krzys9876/ZX_Spectrum_diy/Kicad5/zx2_backplane/zx2_backplane_B.pdf

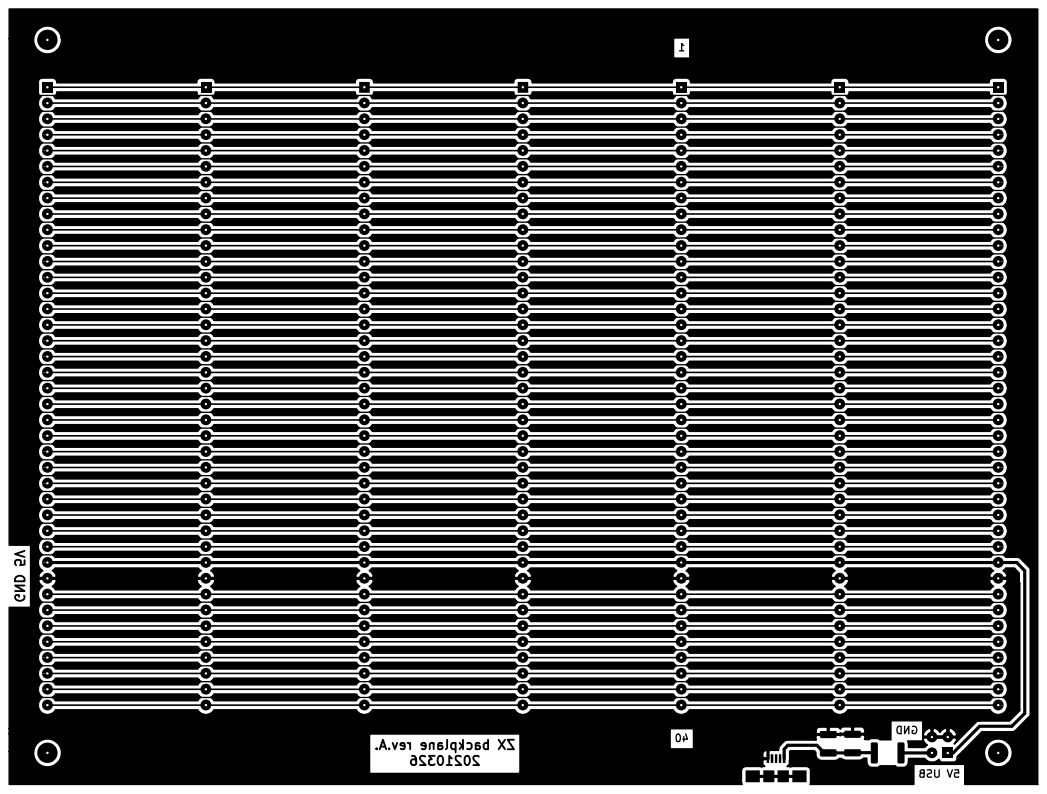
[picture p13: page 1]
