krzys9876/ZX_Spectrum_diy/Kicad5/zx2_clock/zx2_clock_B_err.pdf

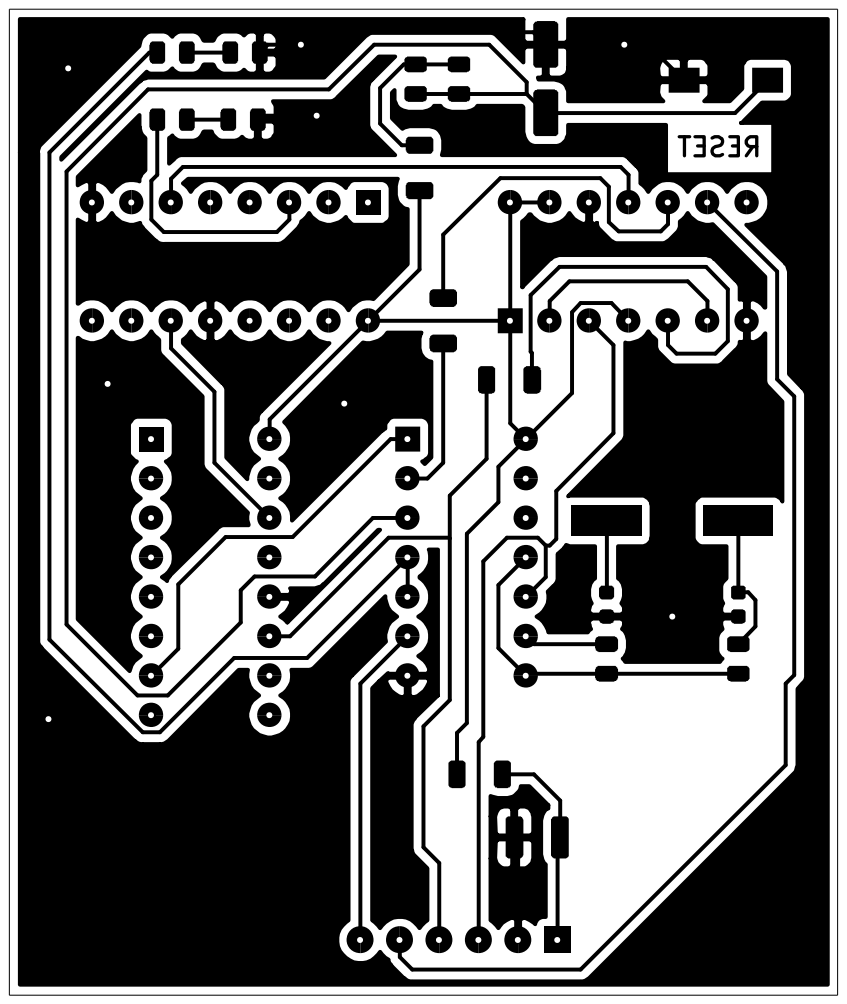
[picture p14: page 1]
