krzys9876/ZX_Spectrum_diy/Kicad5/zx2_clock/zx2_clock_col_err.pdf

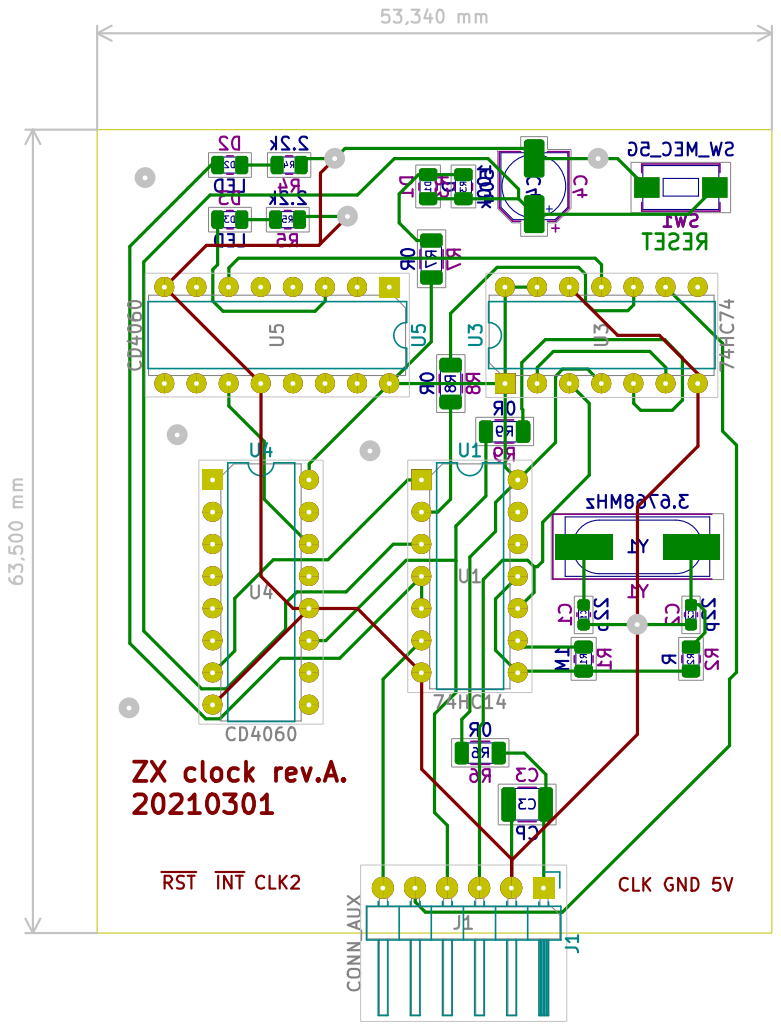
[picture p15: page 1]
