krzys9876/ZX_Spectrum_diy/Kicad5/zx2_clock/zx2_clock_F_err.pdf

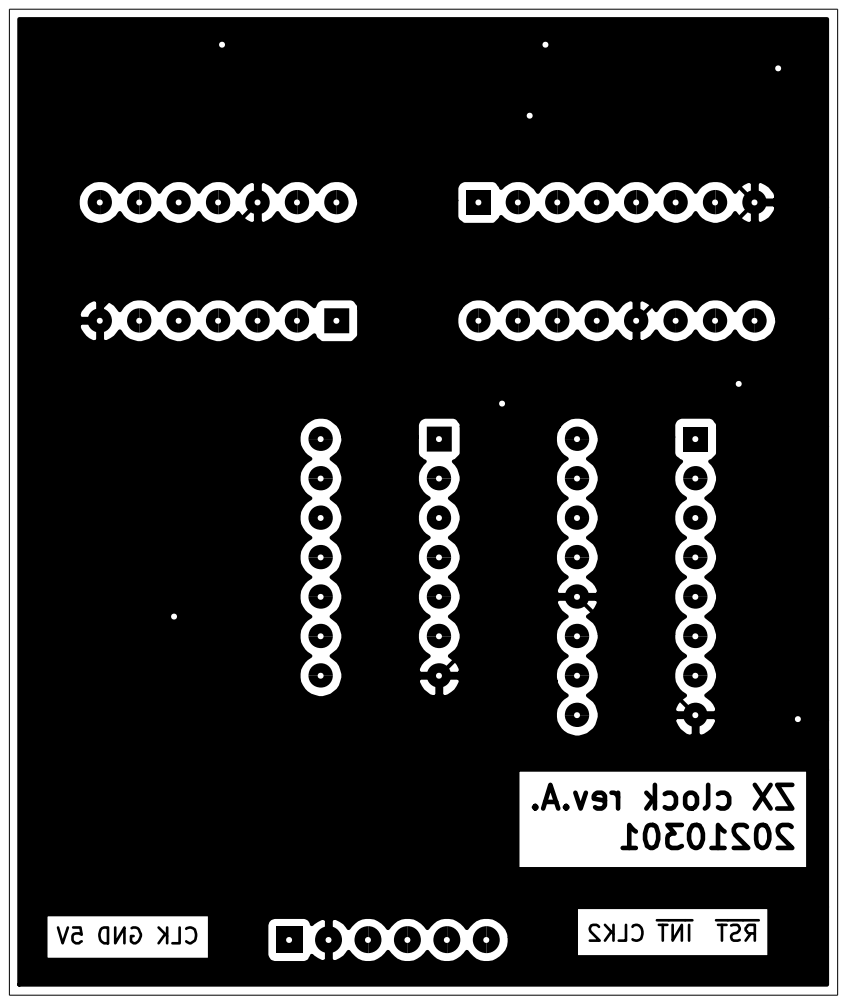
[picture p16: page 1]
