krzys9876/ZX_Spectrum_diy/Kicad5/zx2_cpu/zx2_cpu_B.pdf

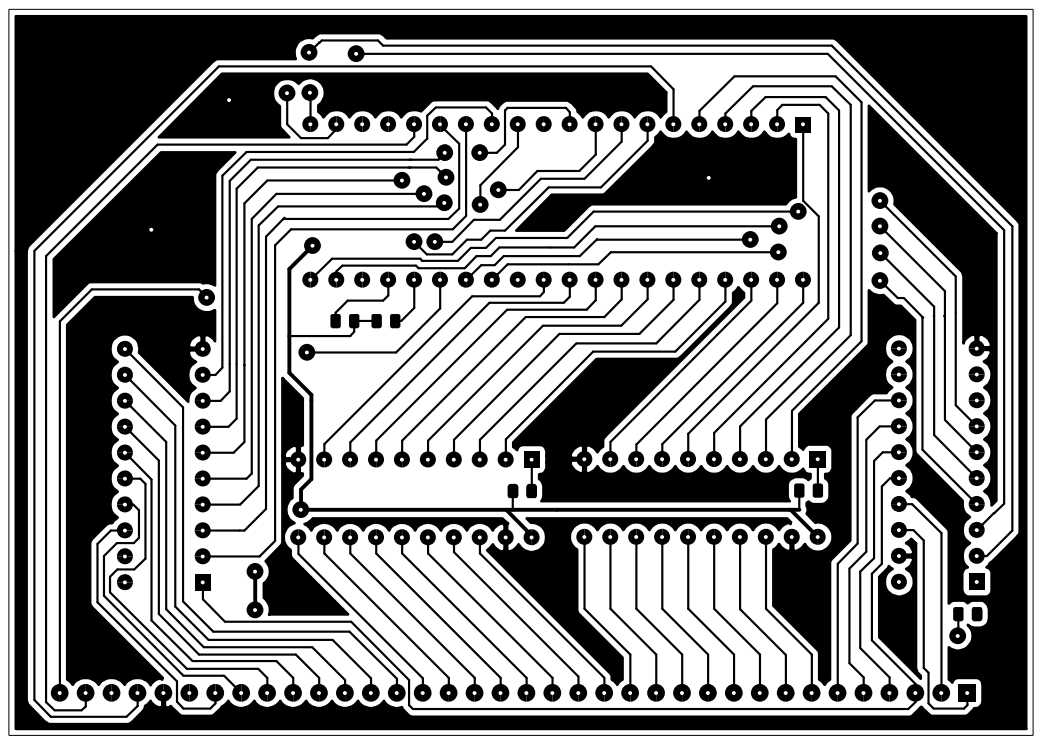
[picture p17: page 1]
