krzys9876/ZX_Spectrum_diy/Kicad5/zx2_cpu/zx2_cpu_col.pdf

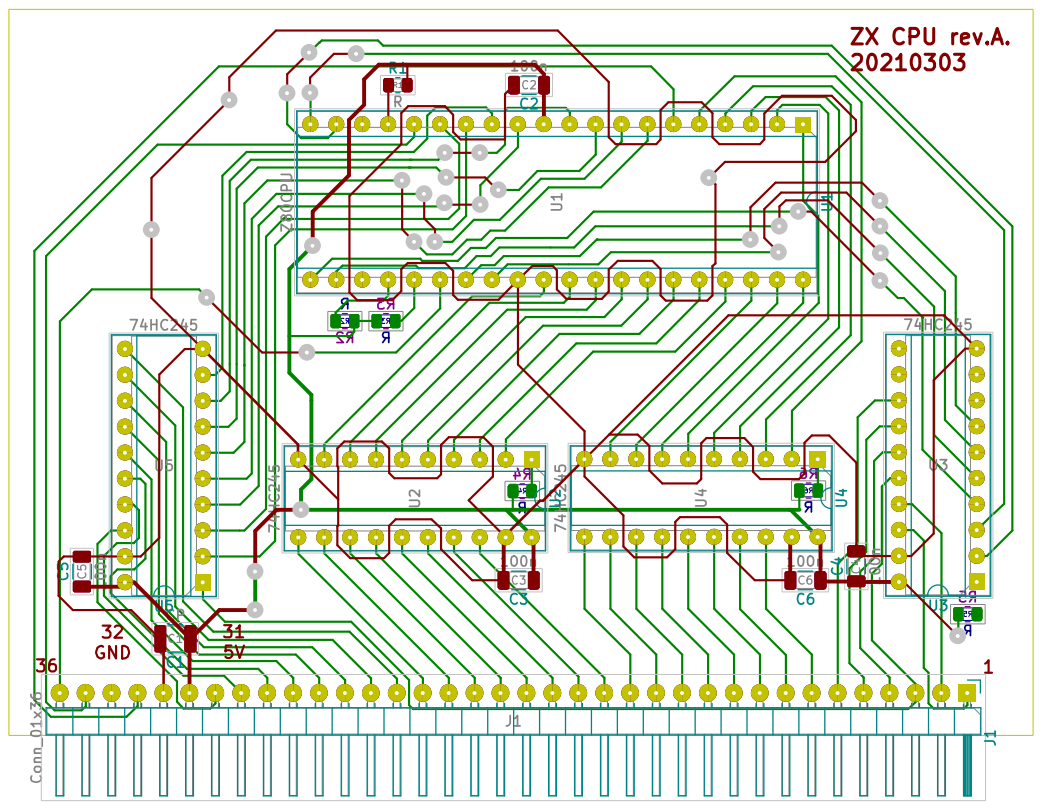
[picture p18: page 1]
