krzys9876/ZX_Spectrum_diy/Kicad5/zx2_cpu/zx2_cpu_F.pdf

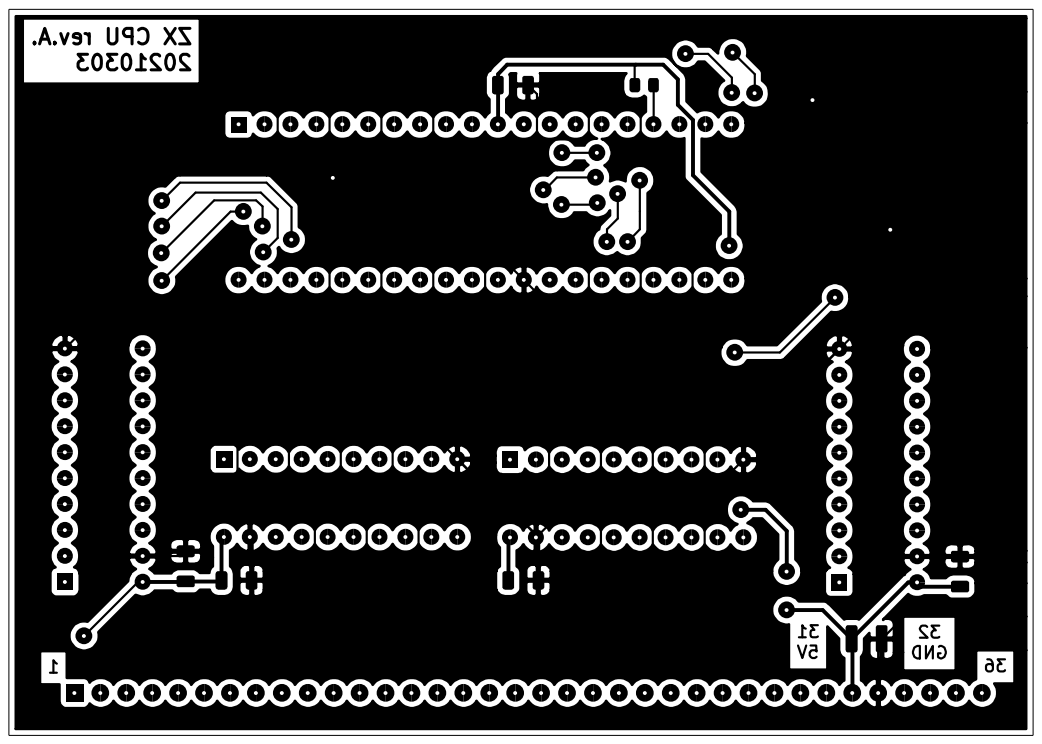
[picture p19: page 1]
