krzys9876/ZX_Spectrum_diy/Kicad5/zx2_fpga_int/zx2_fpga_int_B.pdf

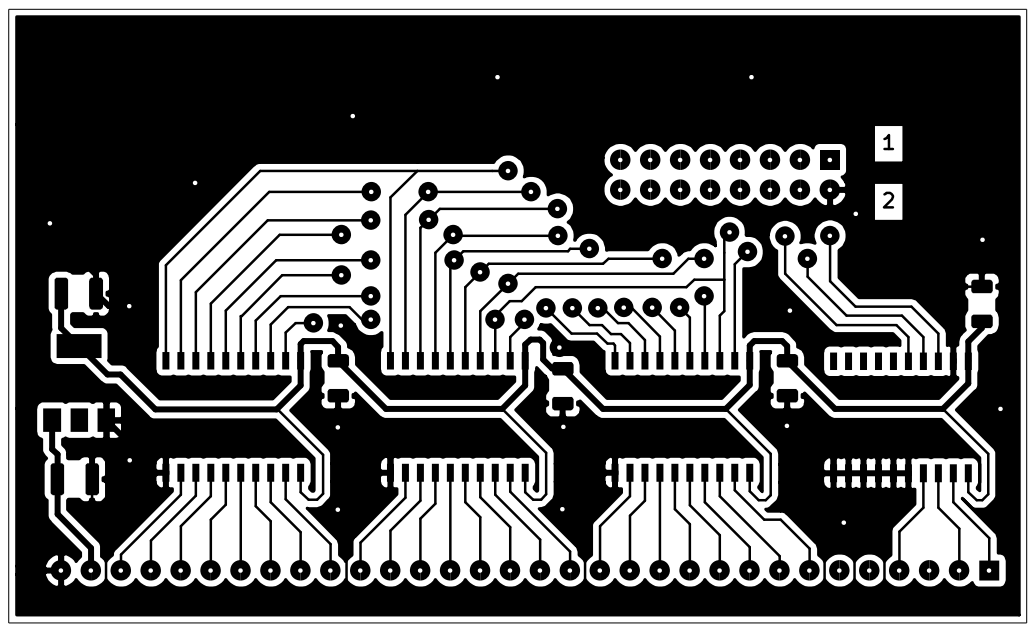
[picture p20: page 1]
