krzys9876/ZX_Spectrum_diy/Kicad5/zx2_fpga_int/zx2_fpga_int_col.pdf

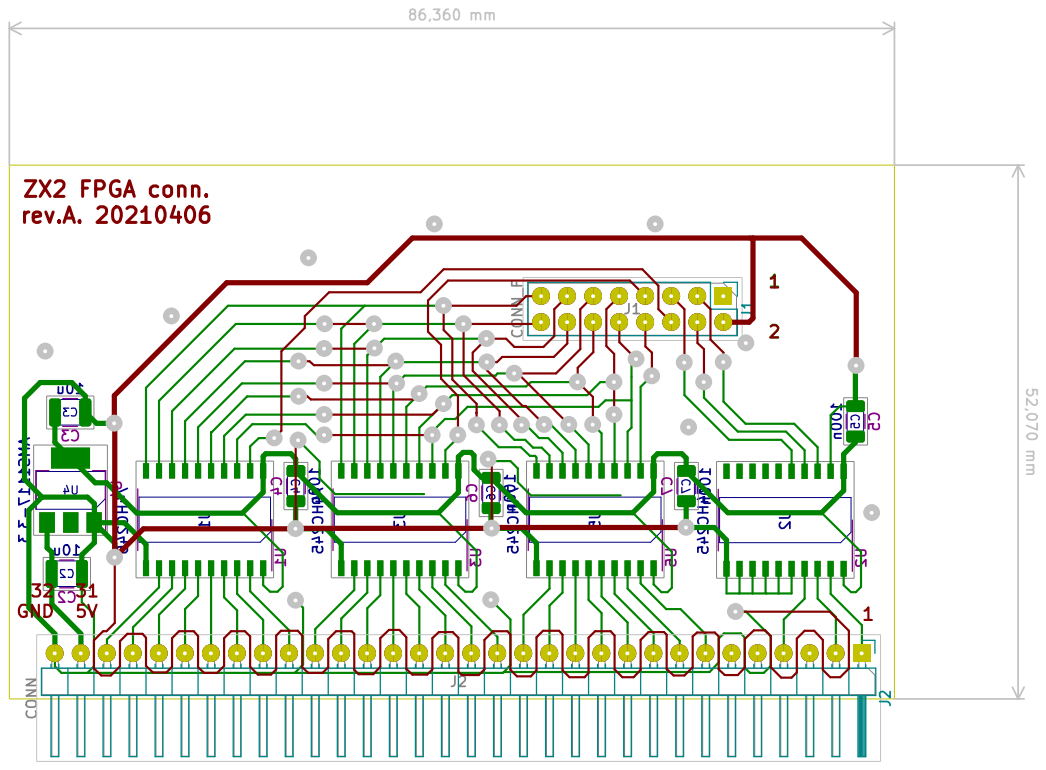
[picture p21: page 1]
