krzys9876/ZX_Spectrum_diy/Kicad5/zx2_fpga_int/zx2_fpga_int_F.pdf

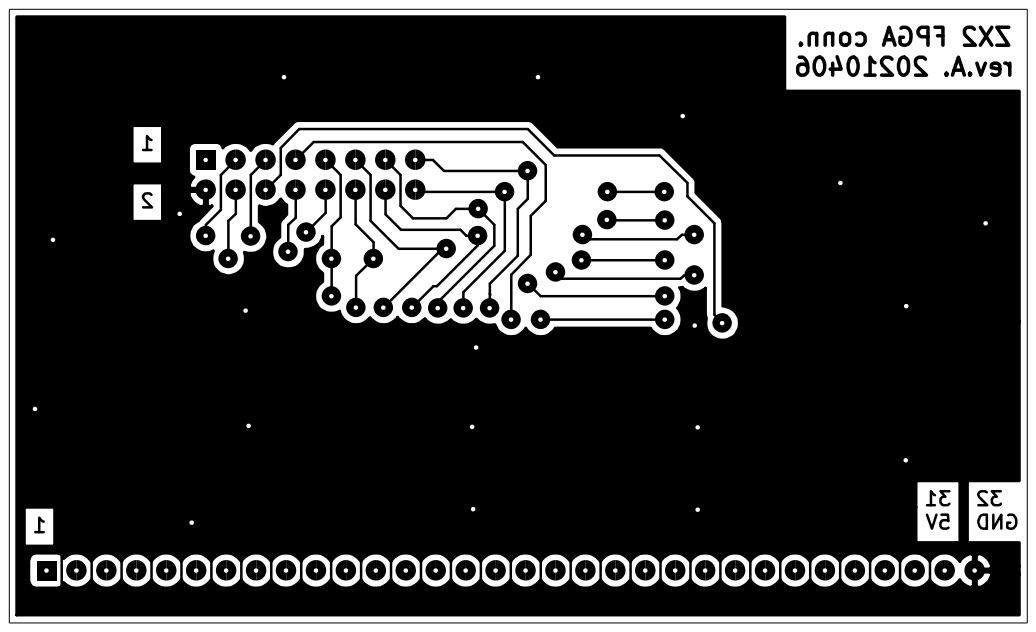
[picture p22: page 1]
