krzys9876/ZX_Spectrum_diy/Kicad5/zx2_keyb_conn/zx2_keyb_conn_B_revB.pdf

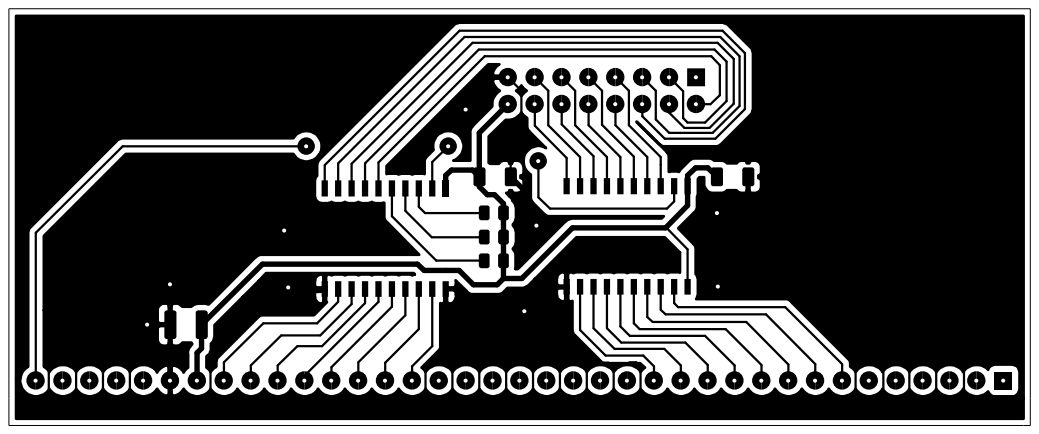
[picture p25: page 1]
