krzys9876/ZX_Spectrum_diy/Kicad5/zx2_keyb_conn/zx2_keyb_conn_col.pdf

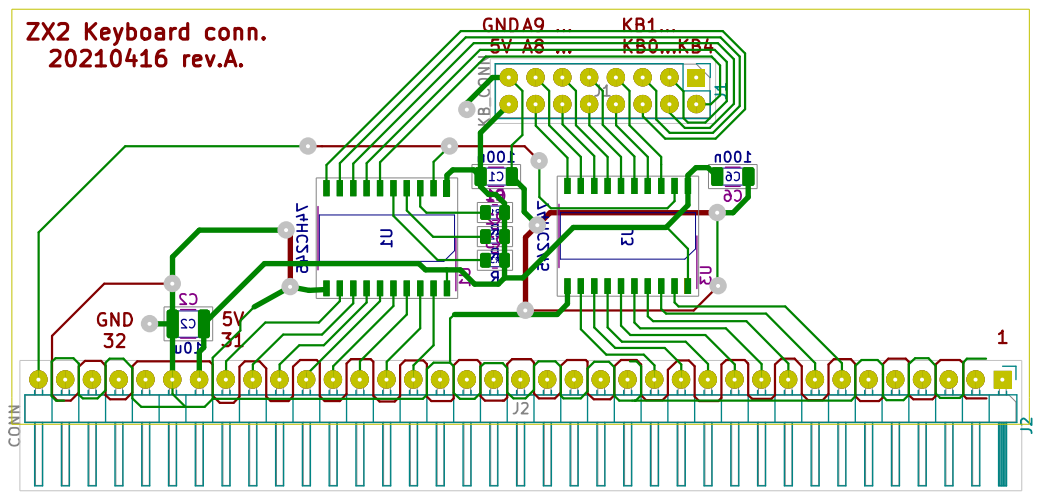
[picture p26: page 1]
