krzys9876/ZX_Spectrum_diy/Kicad5/zx2_keyb_conn/zx2_keyb_conn_col_revB.pdf

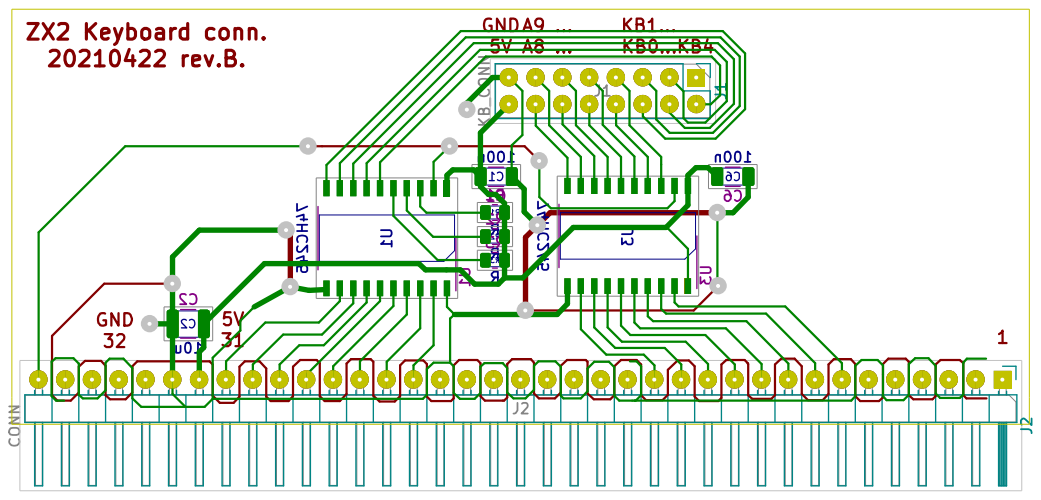
[picture p27: page 1]
