krzys9876/ZX_Spectrum_diy/Kicad5/zx2_keyb_conn/zx2_keyb_conn_F.pdf

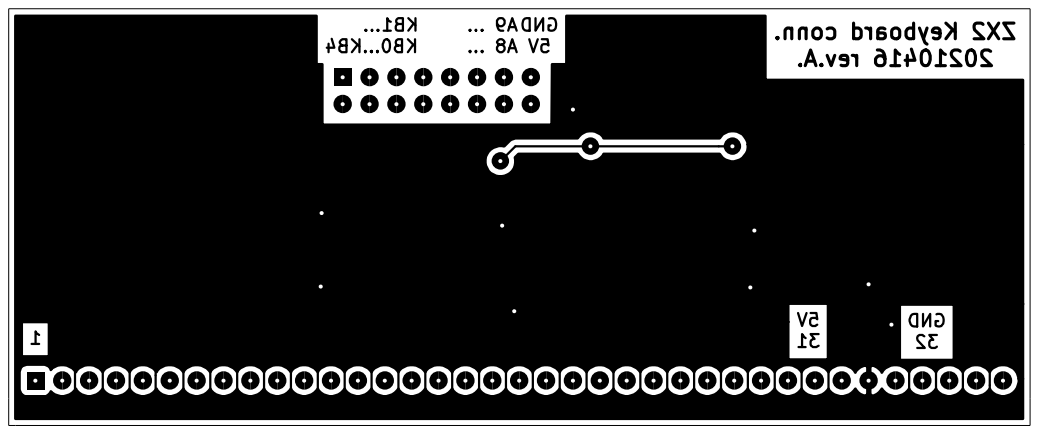
[picture p28: page 1]
