krzys9876/ZX_Spectrum_diy/Kicad5/zx2_keyb_idc/zx2_keyb_idc_F.pdf

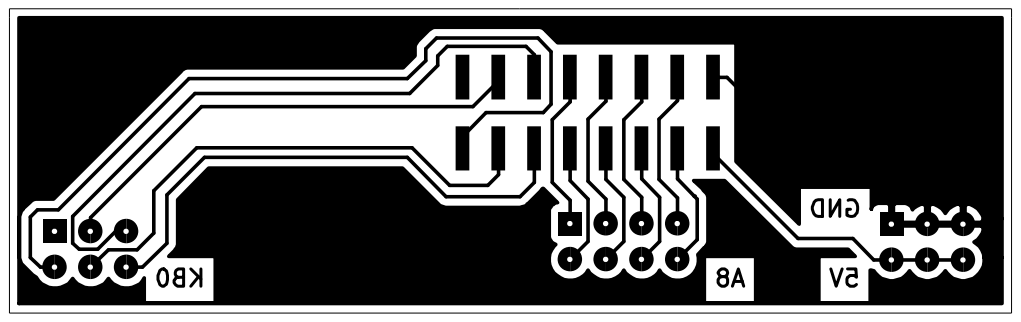
[picture p30: page 1]
