krzys9876/ZX_Spectrum_diy/Kicad5/zx2_mem/zx2_mem_B.pdf

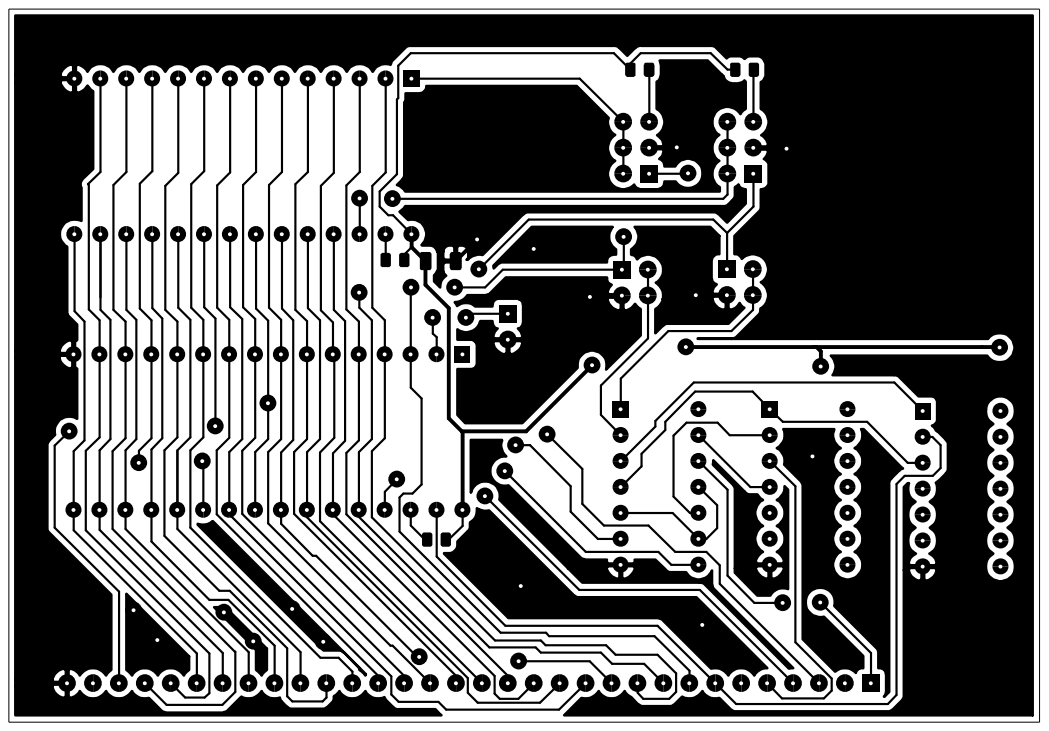
[picture p31: page 1]
