krzys9876/ZX_Spectrum_diy/Kicad5/zx2_mem/zx2_mem_B_rB.pdf

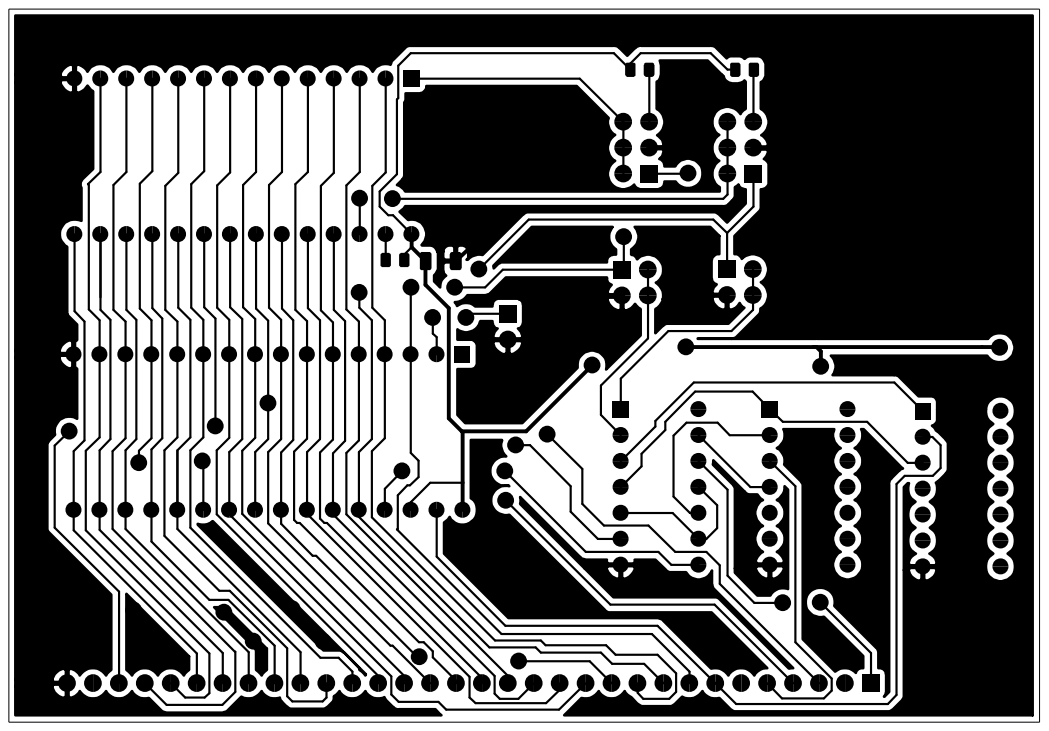
[picture p32: page 1]
