krzys9876/ZX_Spectrum_diy/Kicad5/zx2_mem/zx2_mem_col.pdf

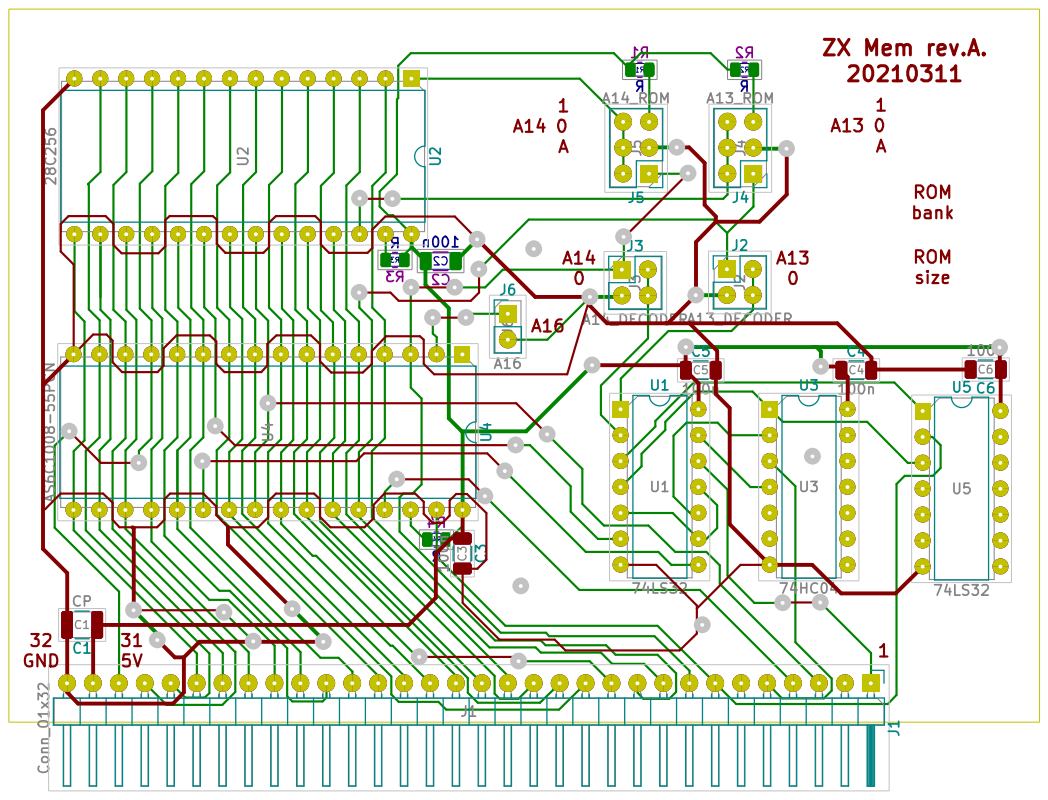
[picture p33: page 1]
