krzys9876/ZX_Spectrum_diy/Kicad5/zx2_mem/zx2_mem_col_rB.pdf

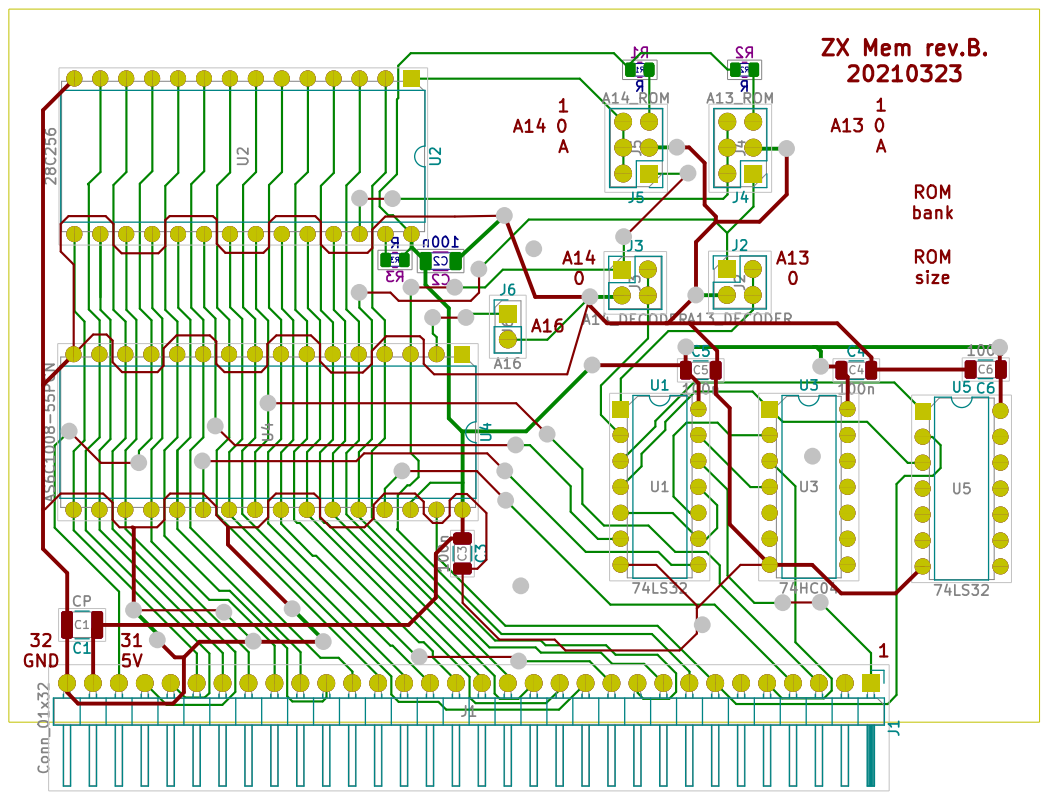
[picture p34: page 1]
