krzys9876/ZX_Spectrum_diy/Kicad5/zx2_mem/zx2_mem_F.pdf

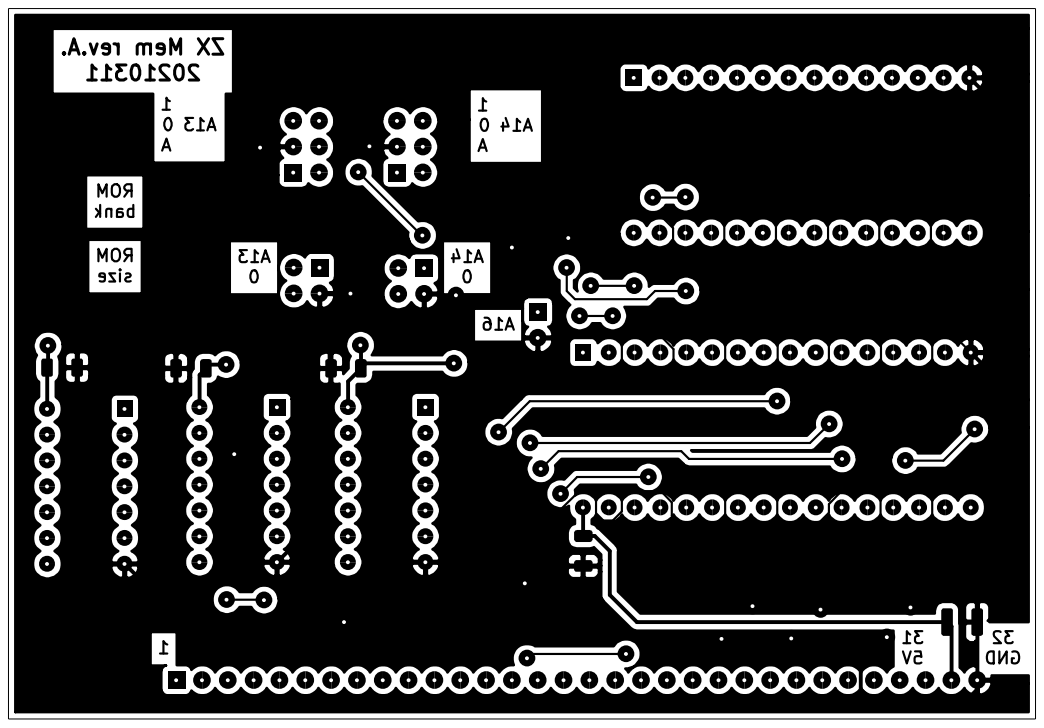
[picture p35: page 1]
