krzys9876/ZX_Spectrum_diy/Kicad5/zx2_mem/zx2_mem_F_rB.pdf

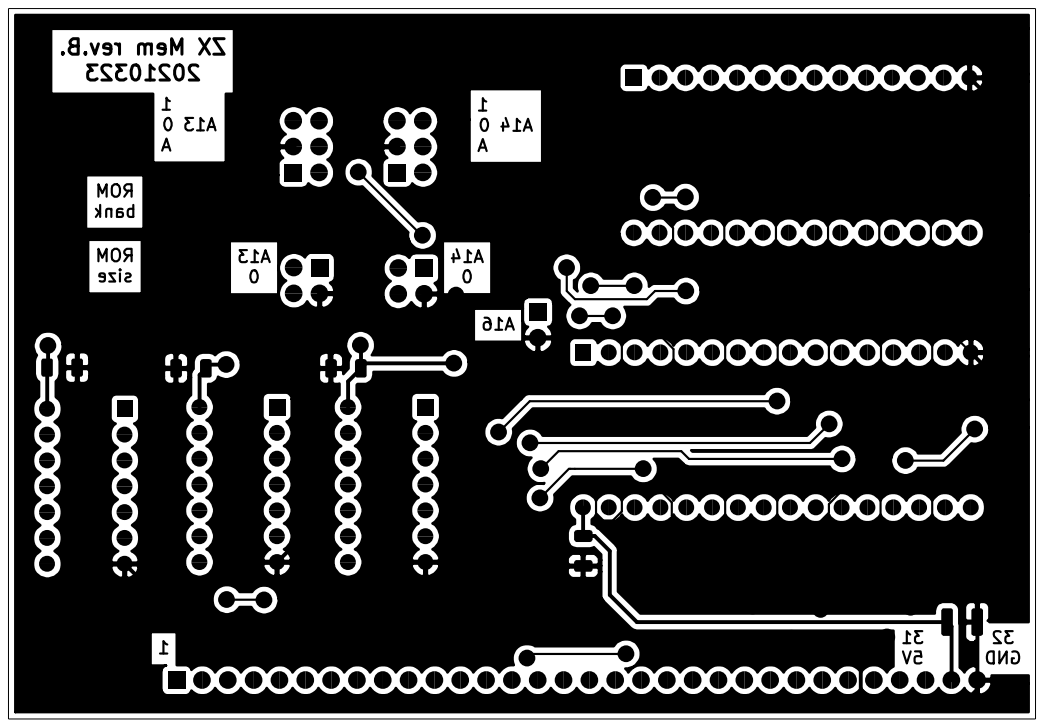
[picture p36: page 1]
