krzys9876/ZX_Spectrum_diy/Kicad5/zx2_uart/zx2_uart_B.pdf

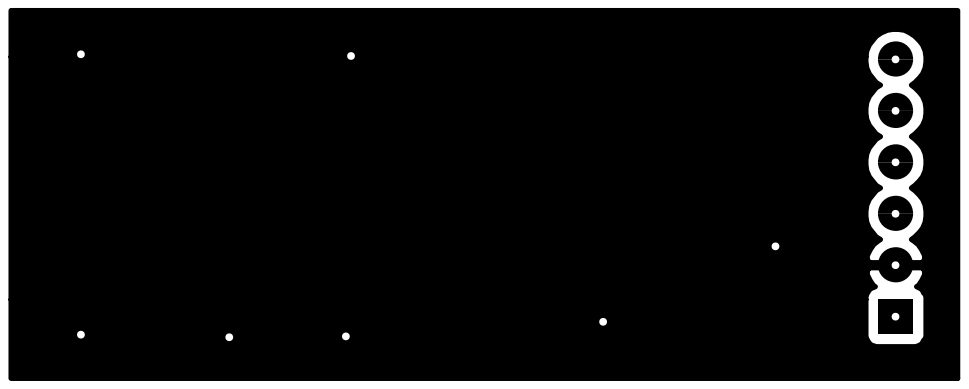
[picture p37: page 1]
