krzys9876/ZX_Spectrum_diy/Kicad5/zx2_uart/zx2_uart_col.pdf

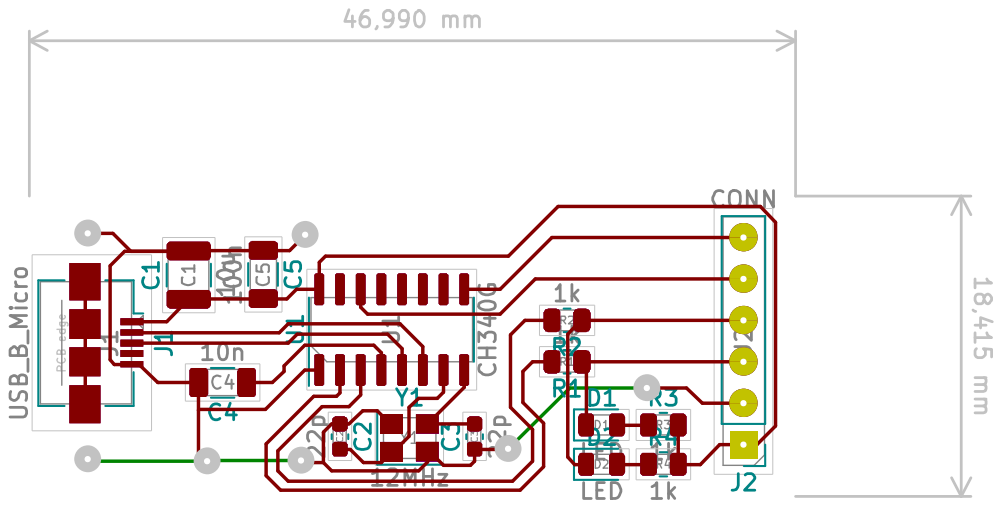
[picture p38: page 1]
