krzys9876/ZX_Spectrum_diy/Kicad5/zx2_uart/zx2_uart_F.pdf

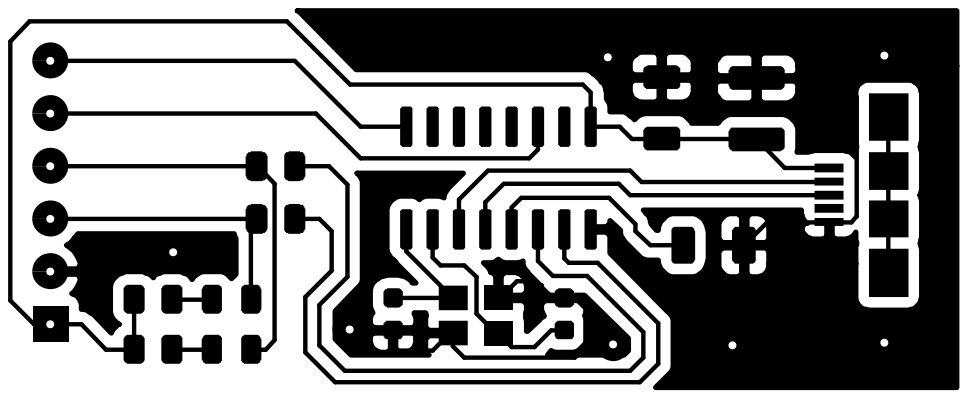
[picture p39: page 1]
